holmesrichards/mtmreverb/Docs/Layout/springReverbRev2_FrontPCB/springReverbRev2_FrontPCB_B.Paste.pdf

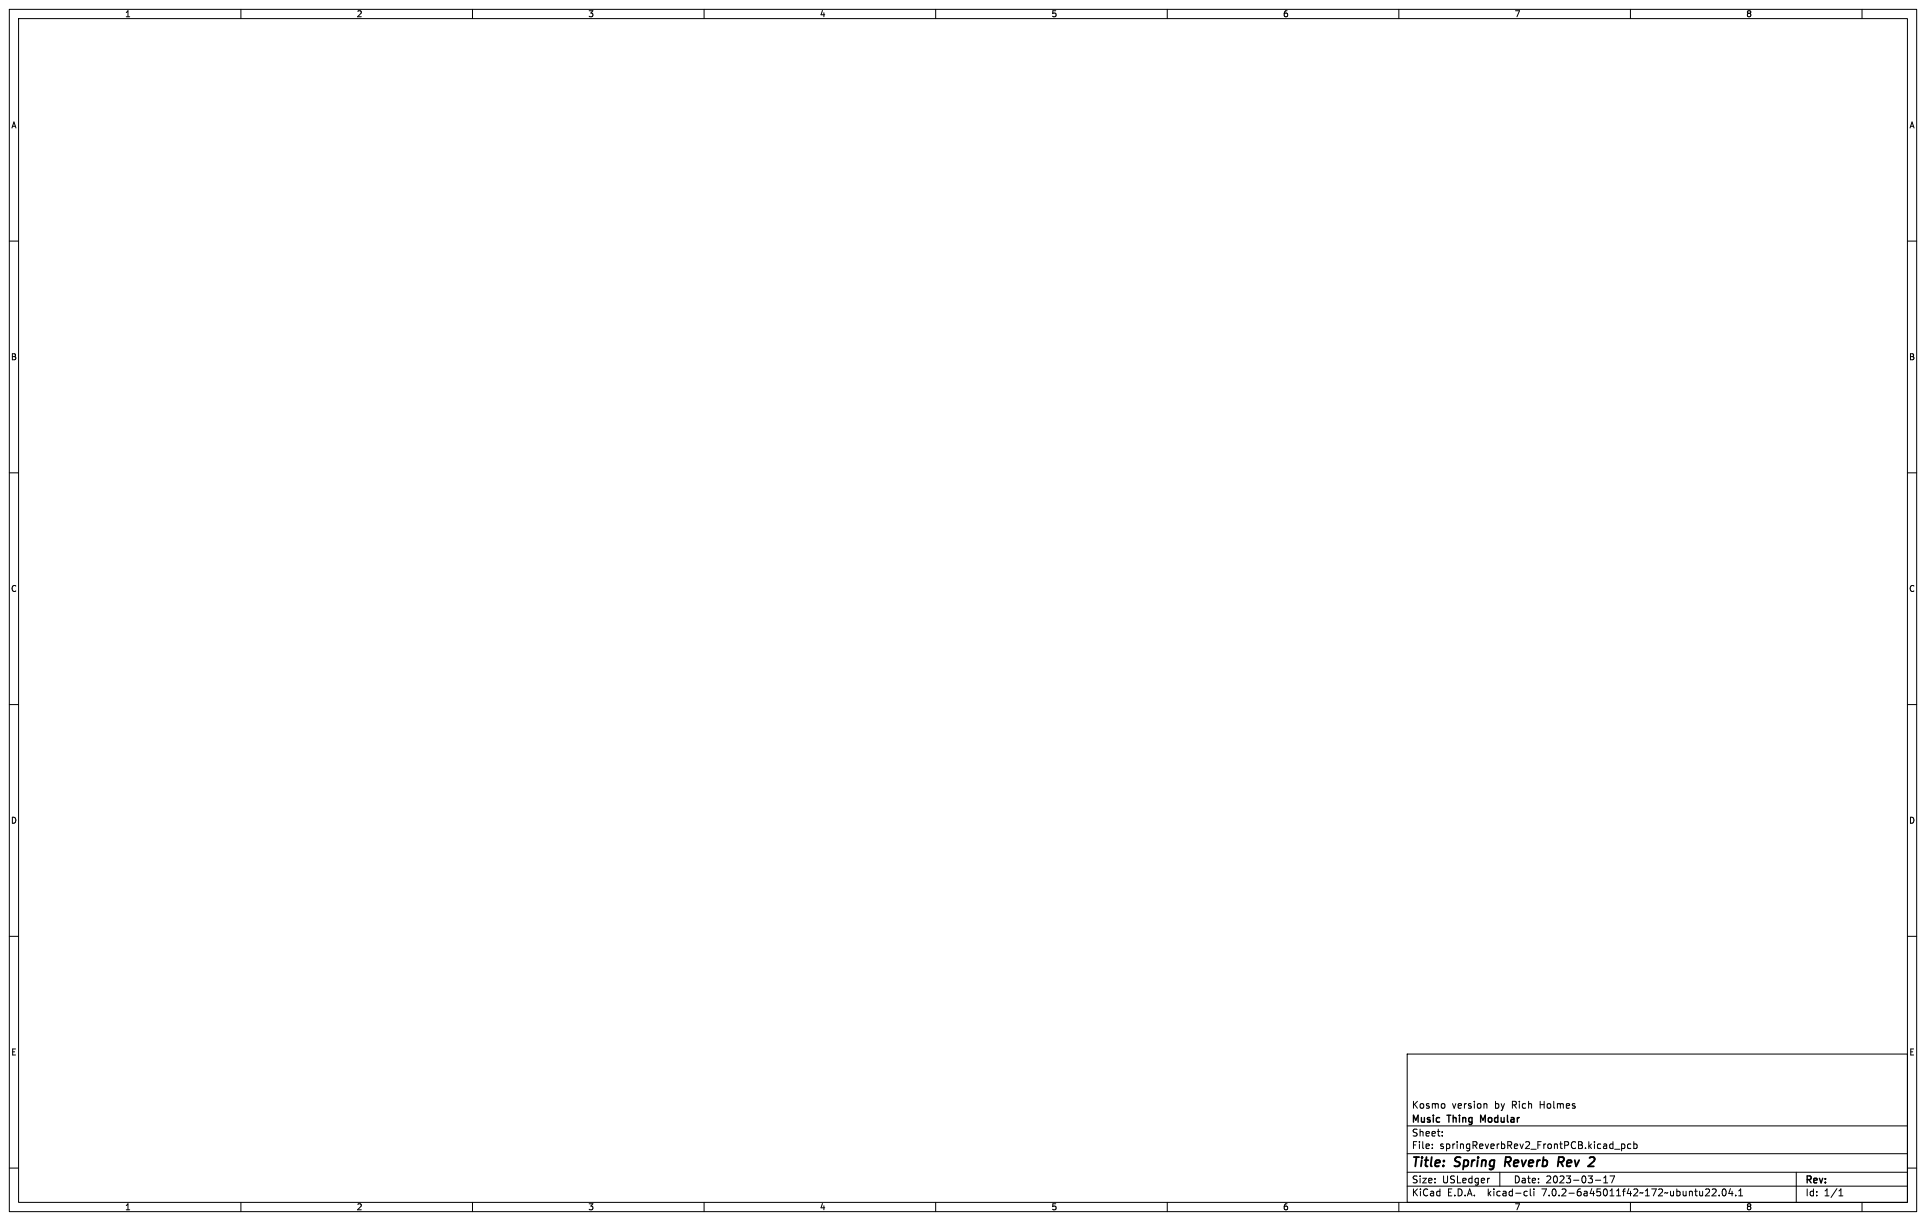
[picture p20: page 1]

Id: 1/1 Title: Spring Reverb Rev 2
