holmesrichards/mtmreverb/Docs/Layout/springReverbRev2_FrontPCB/springReverbRev2_FrontPCB_F.Paste.pdf

Id: 1/1 Title: Spring Reverb Rev 2
