holmesrichards/mtmreverb/Docs/Layout/springReverbRev2_FrontPCB/springReverbRev2_FrontPCB_F.SilkS.pdf

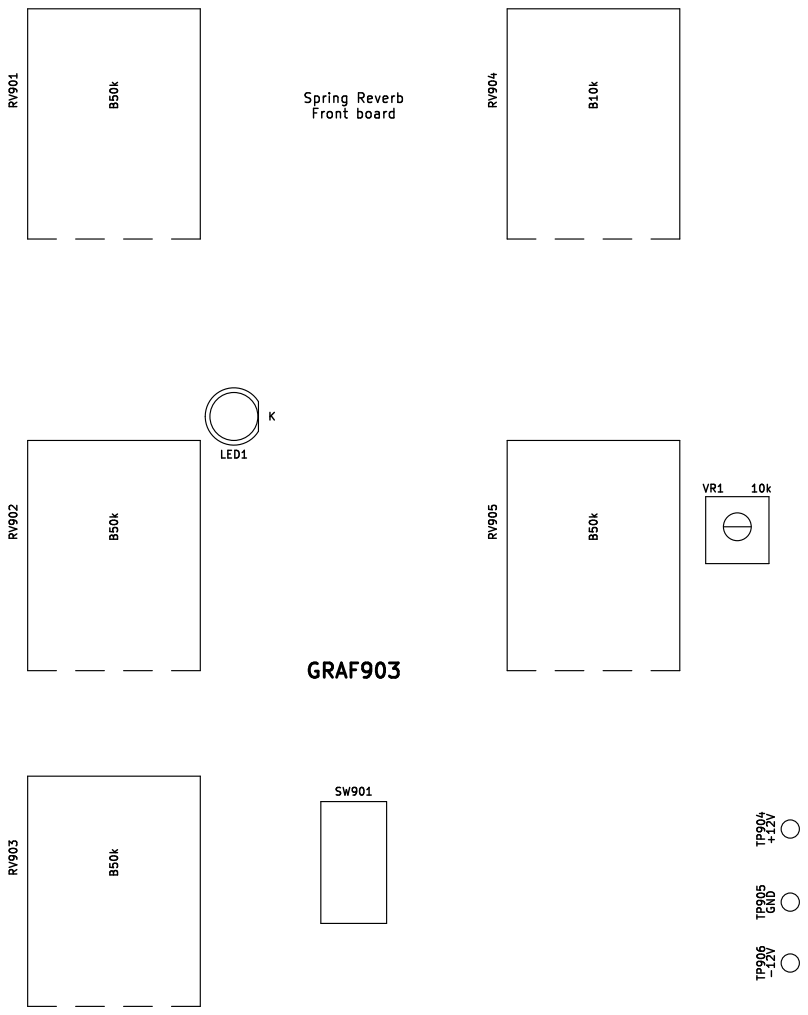
[picture p24: page 1]

Spring Reverb Front board

Id: 1/1 Title: Spring Reverb Rev 2
