holmesrichards/mtmreverb/Docs/Layout/springReverbRev2_panel/springReverbRev2_panel_B.Mask.pdf

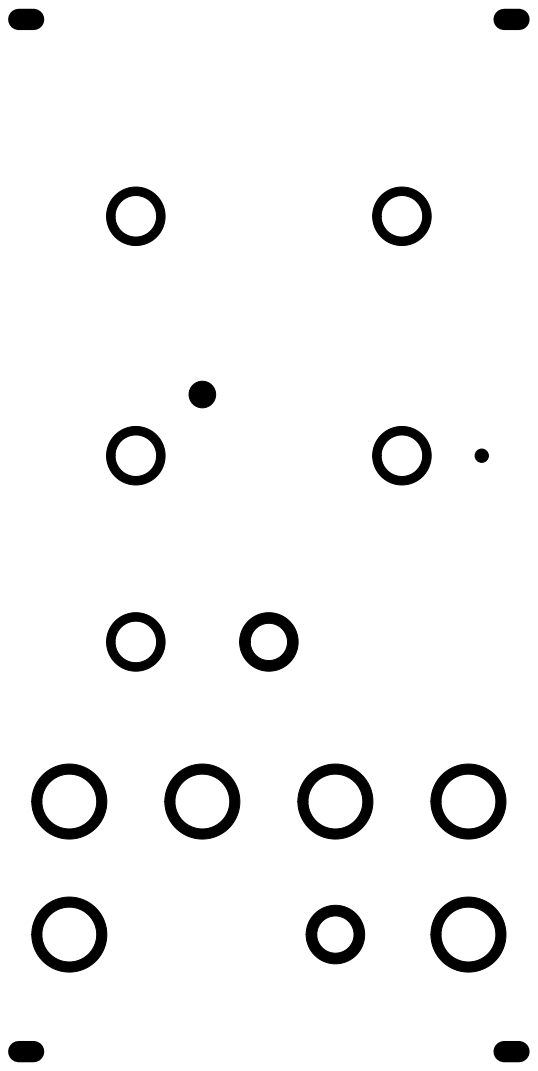
[picture p26: page 1]

Id: 1/1 Title: File: springReverbRev2_panel.kicad_pcb Sheet:
