holmesrichards/mtmreverb/Docs/Layout/springReverbRev2_panel/springReverbRev2_panel_B.Paste.pdf

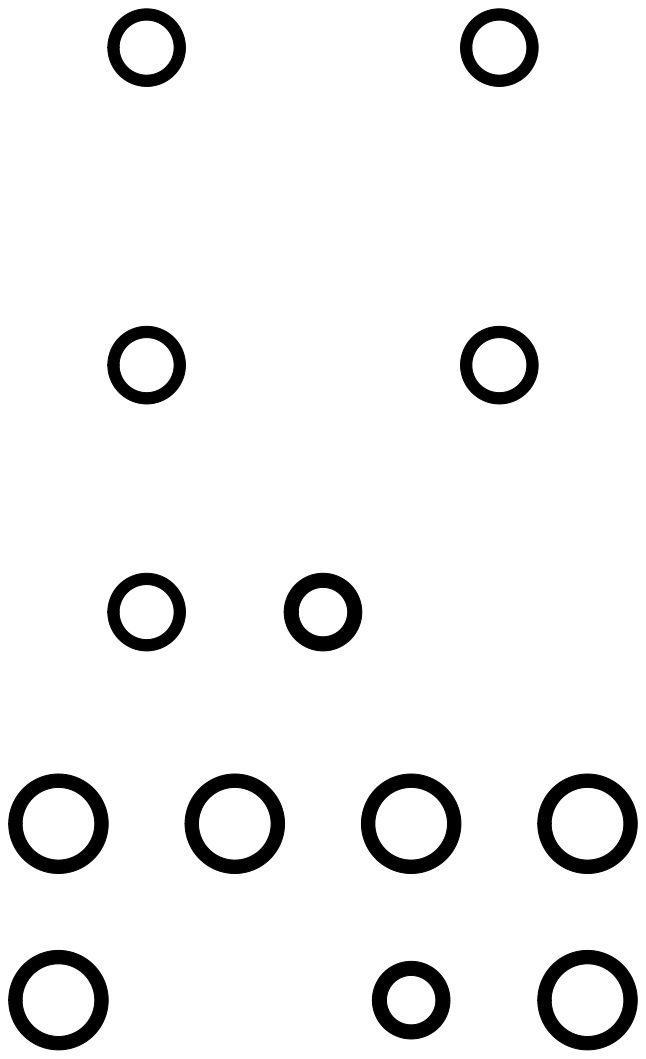
[picture p27: page 1]

Id: 1/1 Title: File: springReverbRev2_panel.kicad_pcb Sheet:
