holmesrichards/mtmreverb/Docs/Layout/springReverbRev2_panel/springReverbRev2_panel_B.SilkS.pdf

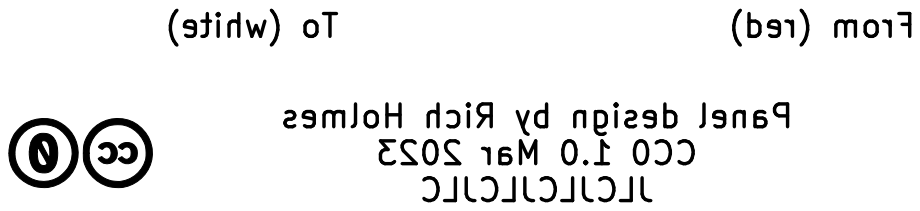
[picture p28: page 1]

From (red) Panel design by Rich Holmes CC0 1.0 Mar 2023

Id: 1/1 Title: File: springReverbRev2_panel.kicad_pcb Sheet:
