holmesrichards/mtmreverb/Docs/Layout/springReverbRev2_panel/springReverbRev2_panel_Edge.Cuts.pdf

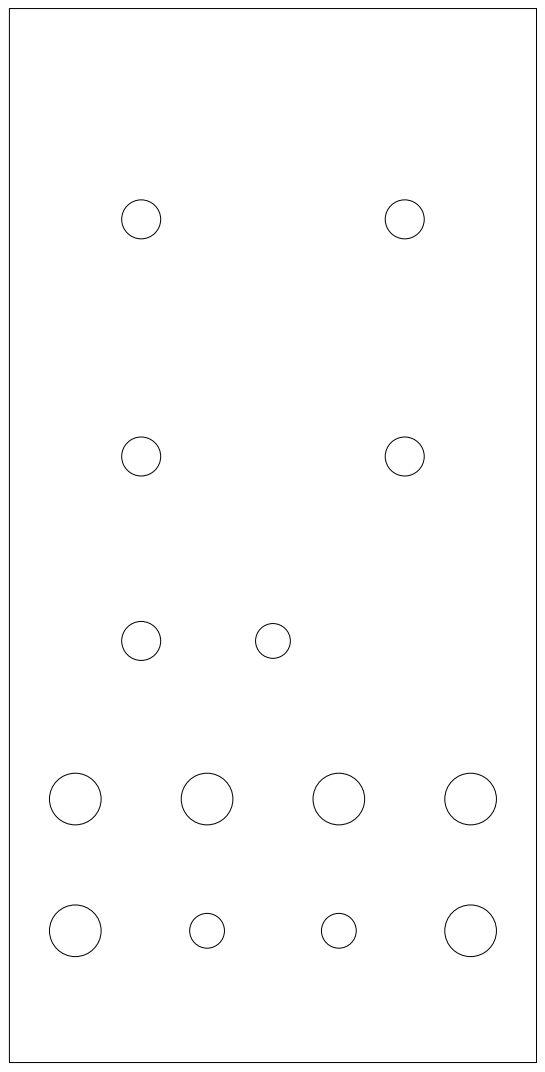
[picture p29: page 1]

Id: 1/1 Title: File: springReverbRev2_panel.kicad_pcb Sheet:
