holmesrichards/mtmreverb/Docs/Layout/springReverbRev2_panel/springReverbRev2_panel_F.Mask.pdf

Id: 1/1 Title: File: springReverbRev2_panel.kicad_pcb Sheet:
